patrickgue/fsimcockpit/Models/ai/images/1b0a5739ef15379fbf4dc0a945f766ee.png

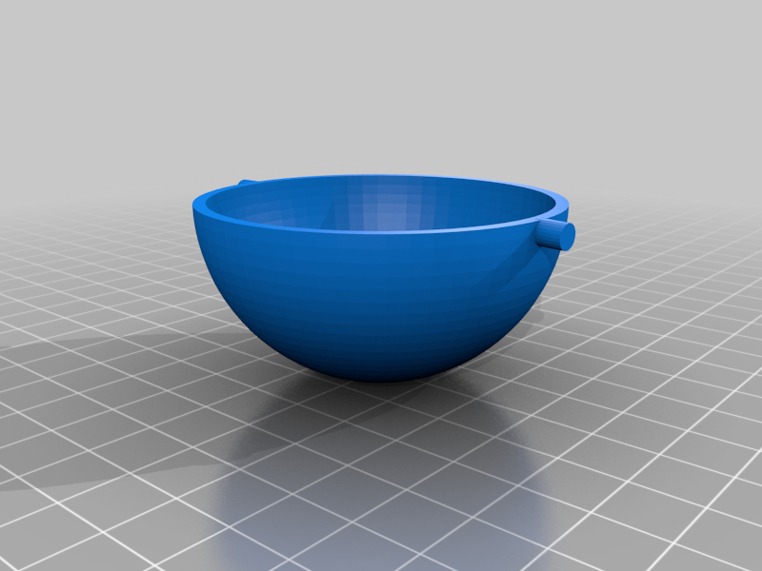
Models/ai/images/1b0a5739ef15379fbf4dc0a945f766ee.png
