patrickgue/fsimcockpit/Models/ai/images/1e4439b8b44afa9f4f896fb0e1ca348d.png

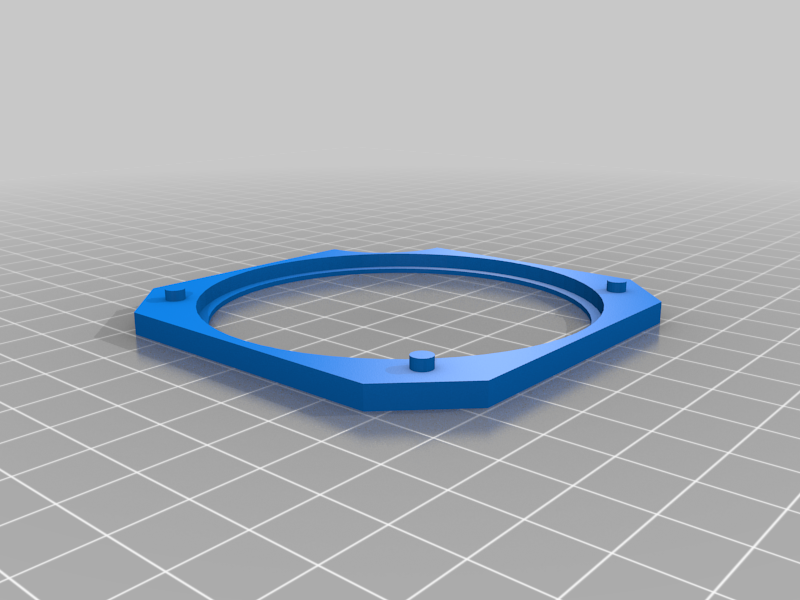
Models/ai/images/1e4439b8b44afa9f4f896fb0e1ca348d.png
