patrickgue/fsimcockpit/Models/ai/images/02c6412a4f1afc17a5a2229d6d05a12a.png

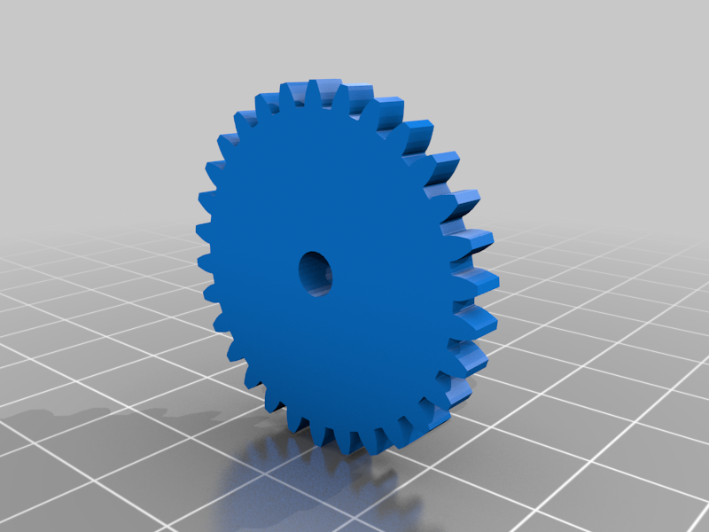
Models/ai/images/02c6412a4f1afc17a5a2229d6d05a12a.png
