patrickgue/fsimcockpit/Models/ai/images/3a77de7b587de0e3436b201ad0739e6e.png

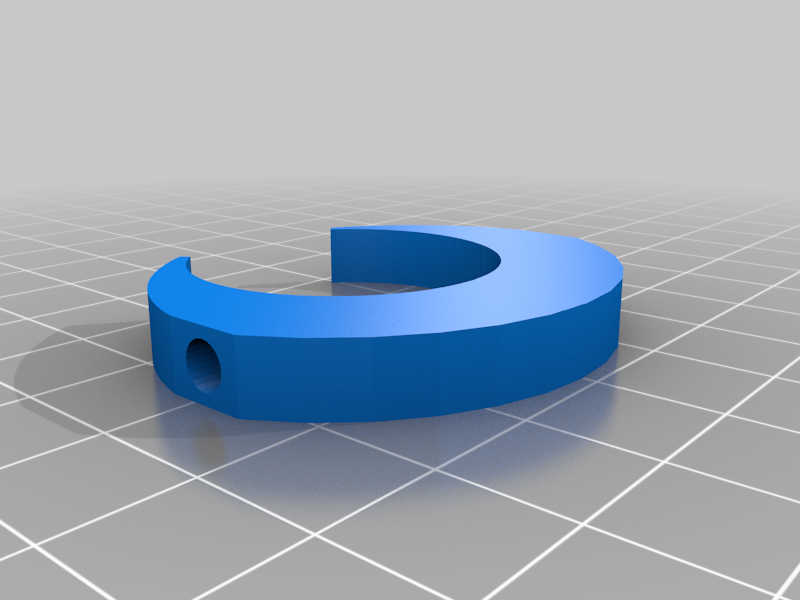
Models/ai/images/3a77de7b587de0e3436b201ad0739e6e.png
