patrickgue/fsimcockpit/Models/ai/images/6ea9e44ec9cb2694fbe0ab6ae0526416.png

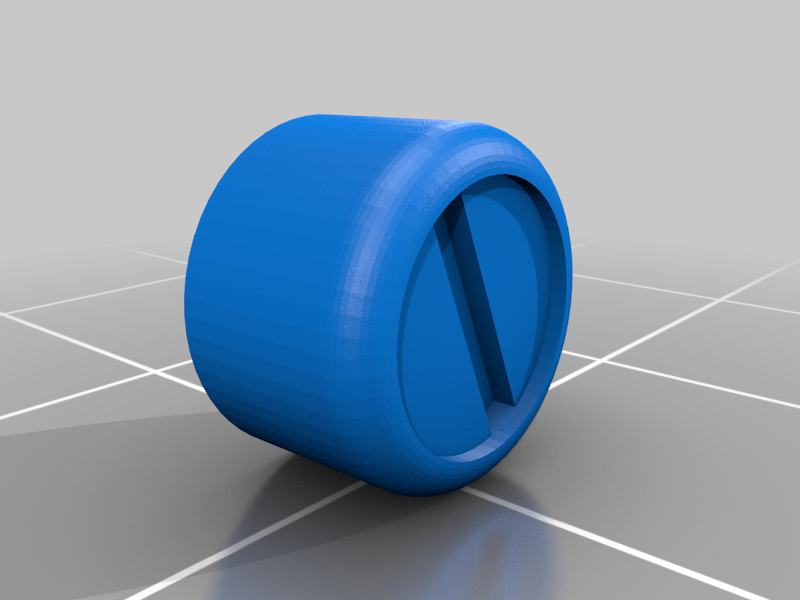
Models/ai/images/6ea9e44ec9cb2694fbe0ab6ae0526416.png
