patrickgue/fsimcockpit/Models/ai/images/9bbd3e1e0be2ce5231e5939fdd35f54f.png

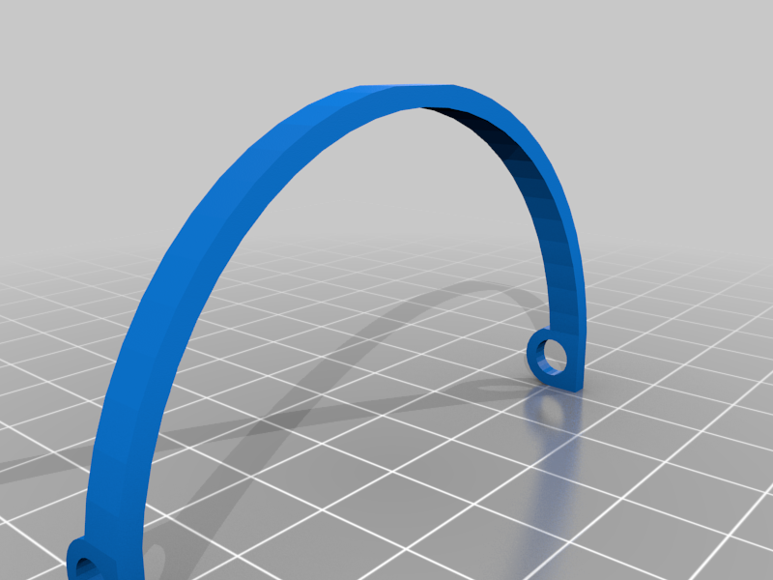
Models/ai/images/9bbd3e1e0be2ce5231e5939fdd35f54f.png
