patrickgue/fsimcockpit/Models/ai/images/9d65d15d78d8a212db82cd6689131c01.png

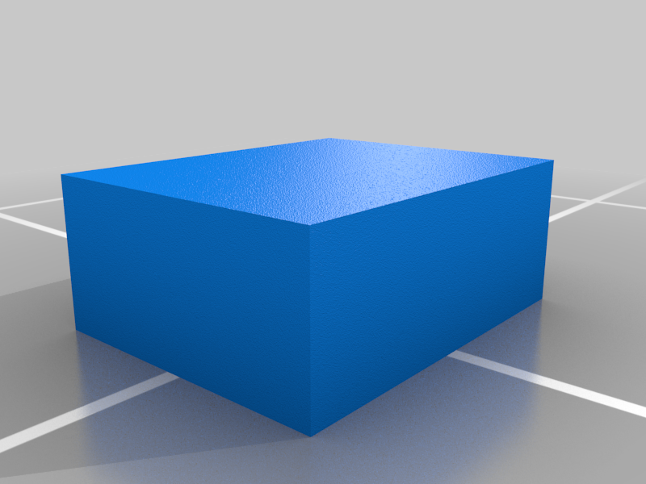
Models/ai/images/9d65d15d78d8a212db82cd6689131c01.png
