patrickgue/fsimcockpit/Models/ai/images/497fff0eb1eede1f7c7d94e4efdf7a6d.png

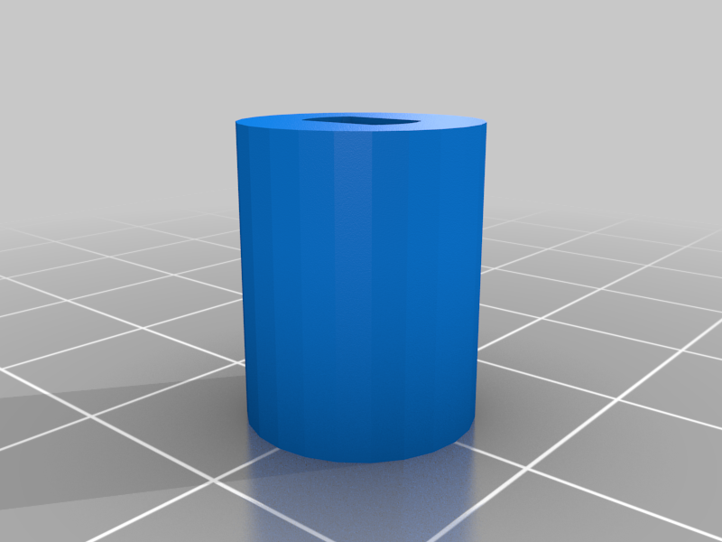
Models/ai/images/497fff0eb1eede1f7c7d94e4efdf7a6d.png
