patrickgue/fsimcockpit/Models/ai/images/996b78e1af478235ca2ef95079a0255b.png

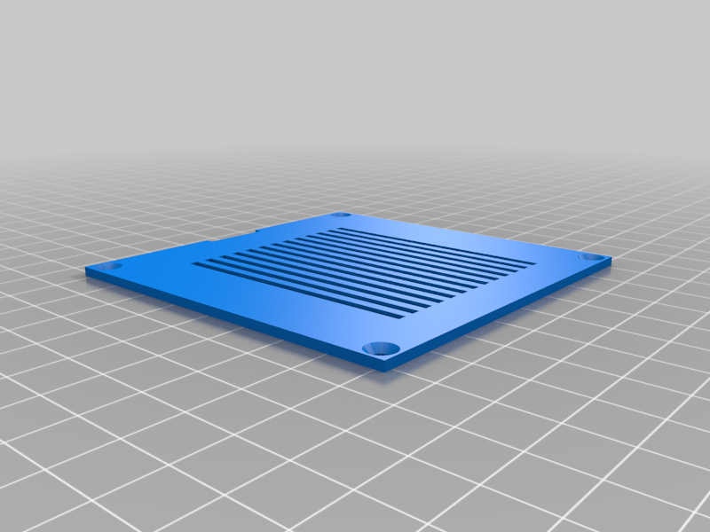
Models/ai/images/996b78e1af478235ca2ef95079a0255b.png
