patrickgue/fsimcockpit/Models/ai/images/b6f1c5f29eb557028f5184abd817bedb.png

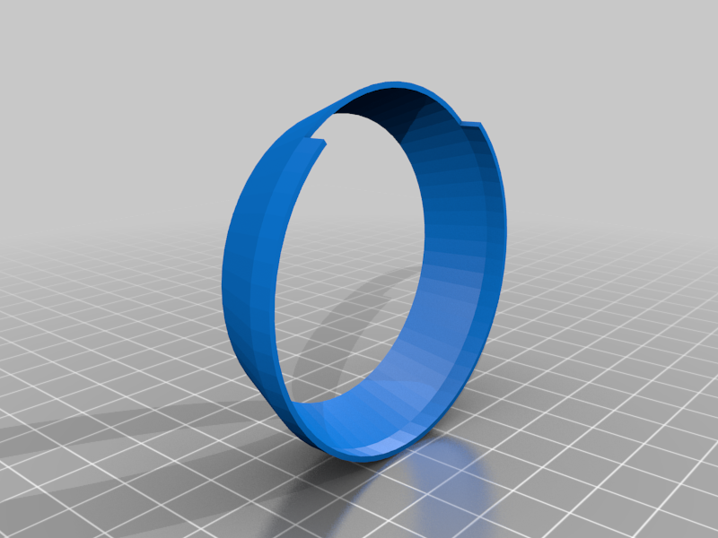
Models/ai/images/b6f1c5f29eb557028f5184abd817bedb.png
