patrickgue/fsimcockpit/Models/ai/images/Bank_Angle.jpg

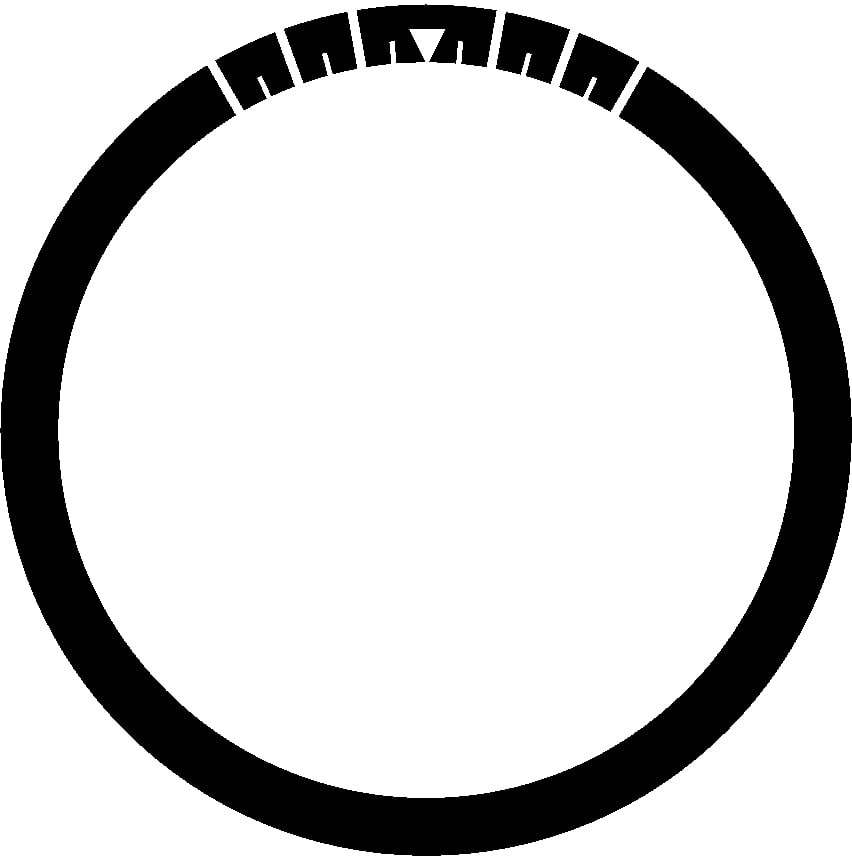
Models/ai/images/Bank_Angle.jpg
