patrickgue/fsimcockpit/Models/ai/images/de8ef12720e9b7bbc3c7db81c315f879.png

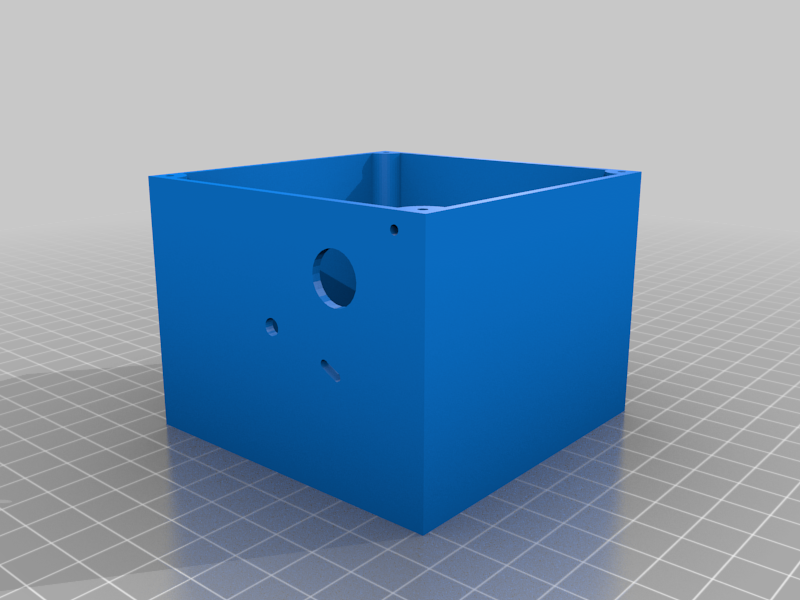
Models/ai/images/de8ef12720e9b7bbc3c7db81c315f879.png
