patrickgue/fsimcockpit/Models/ai/images/df47952833d656812641ab8248f8aa33.png

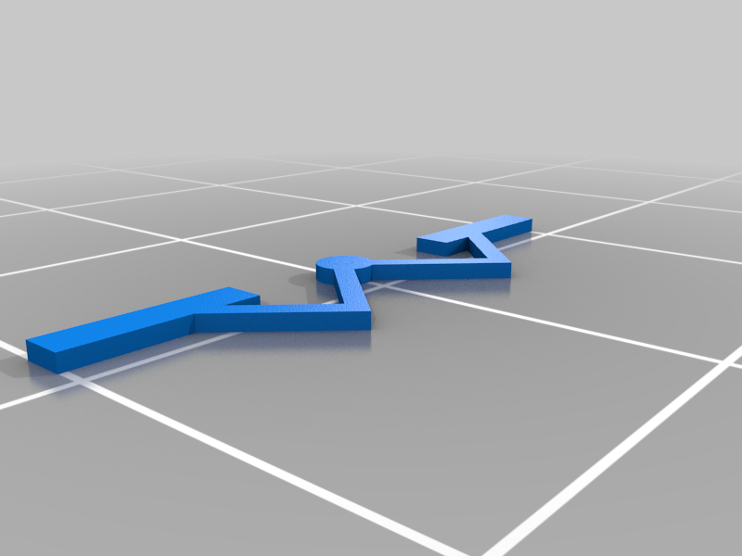
Models/ai/images/df47952833d656812641ab8248f8aa33.png
