patrickgue/fsimcockpit/Models/ai/images/Download_3.png

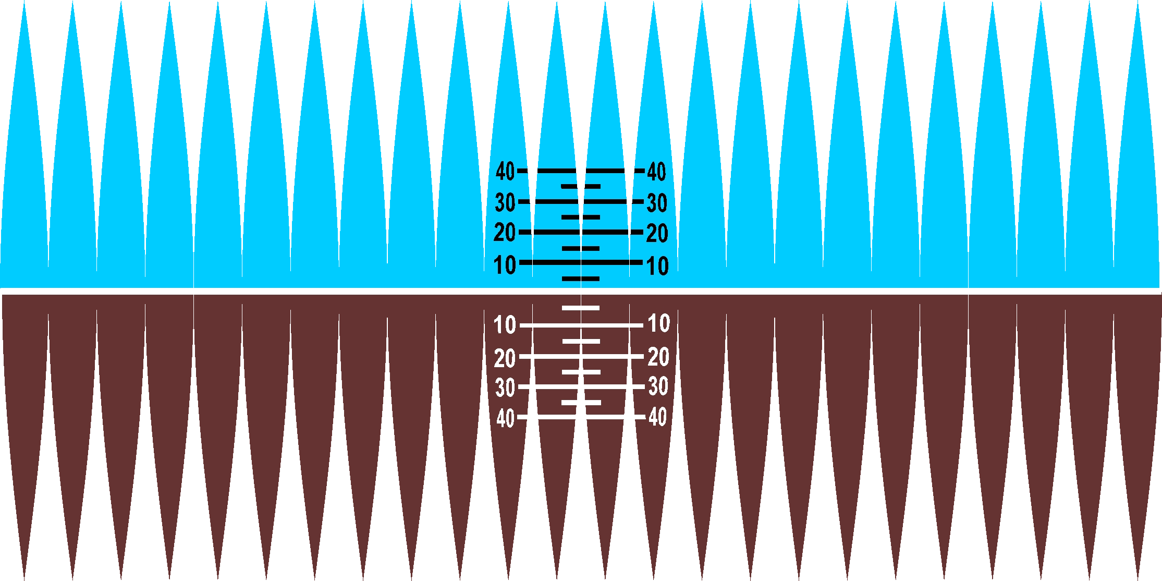
Models/ai/images/Download_3.png
