patrickgue/fsimcockpit/Models/tc/images/941b54a7-352c-473a-afa9-f229a11ba6b9.jpg

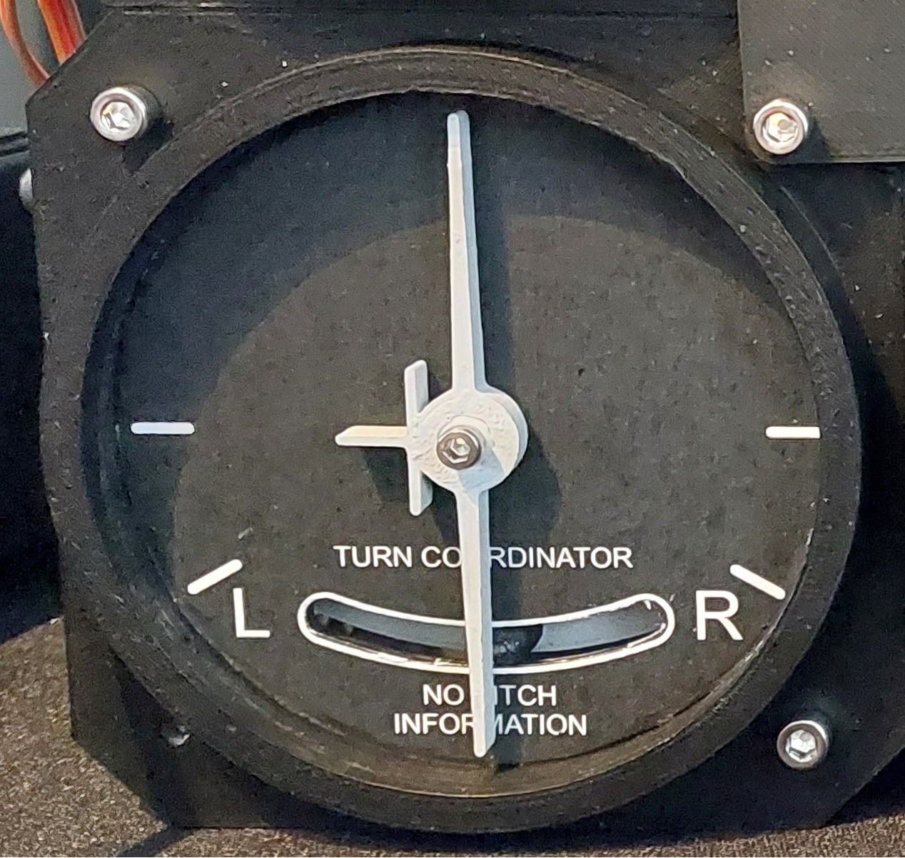
Models/tc/images/941b54a7-352c-473a-afa9-f229a11ba6b9.jpg
