patrickgue/fsimcockpit/Models/tc/images/90883c77-fded-4542-9856-6aad363a4fbb.png

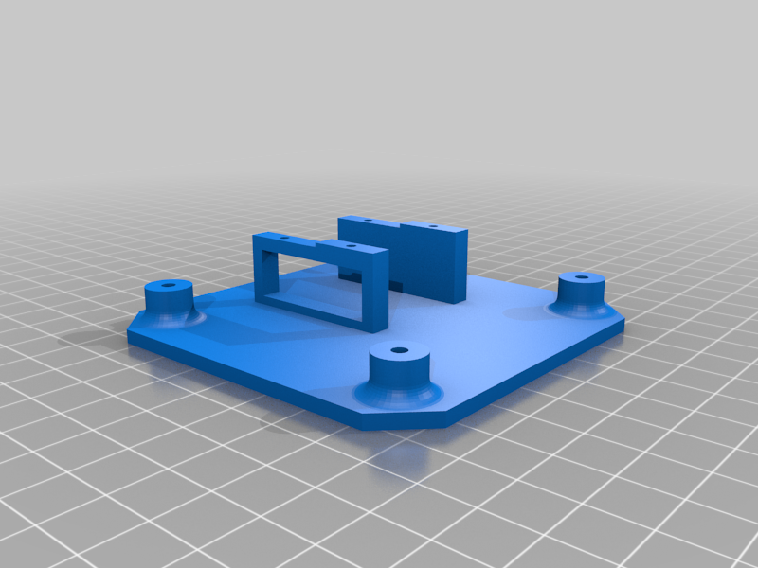
Models/tc/images/90883c77-fded-4542-9856-6aad363a4fbb.png
