patrickgue/fsimcockpit/Models/tc/images/bf2bf9c6-6777-4b66-9cf1-4f259d72259a.png

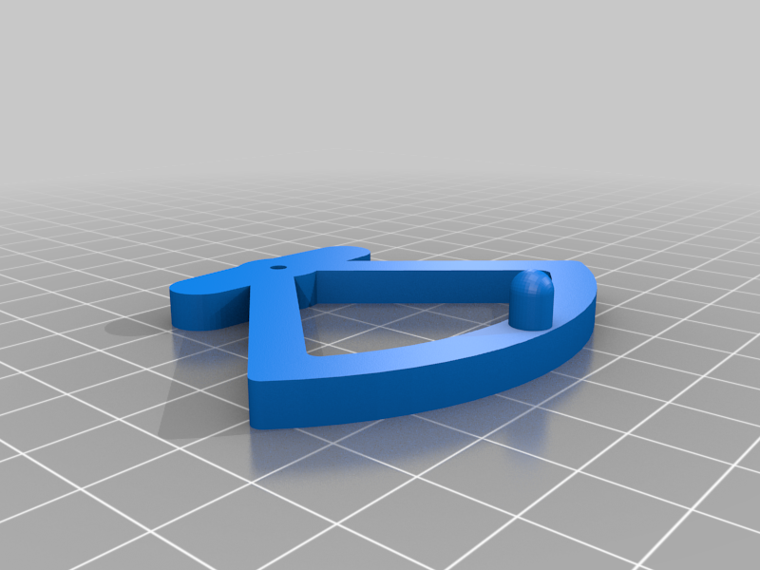
Models/tc/images/bf2bf9c6-6777-4b66-9cf1-4f259d72259a.png
