patrickgue/fsimcockpit/Models/vsi_as/Vertical velocity indicator for flight simulator - 6637015/images/29d1b277-3d54-4ff1-81d7-2cb92e95f4e1.jpg

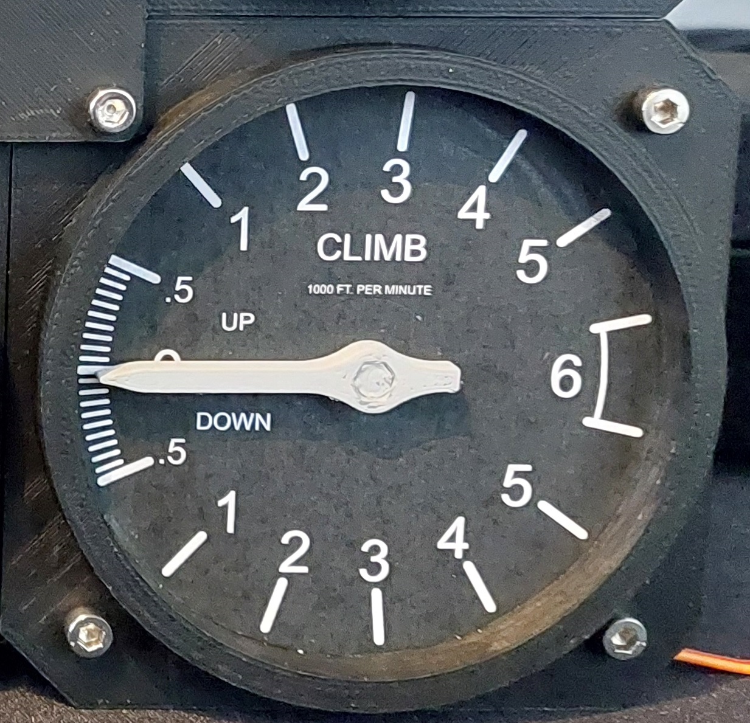
Models/vsi_as/Vertical velocity indicator for flight simulator - 6637015/images/29d1b277-3d54-4ff1-81d7-2cb92e95f4e1.jpg
