patrickgue/fsimcockpit/Models/vsi_as/Vertical velocity indicator for flight simulator - 6637015/images/589b4585-1702-4620-8059-6b79ba6a5d64.png

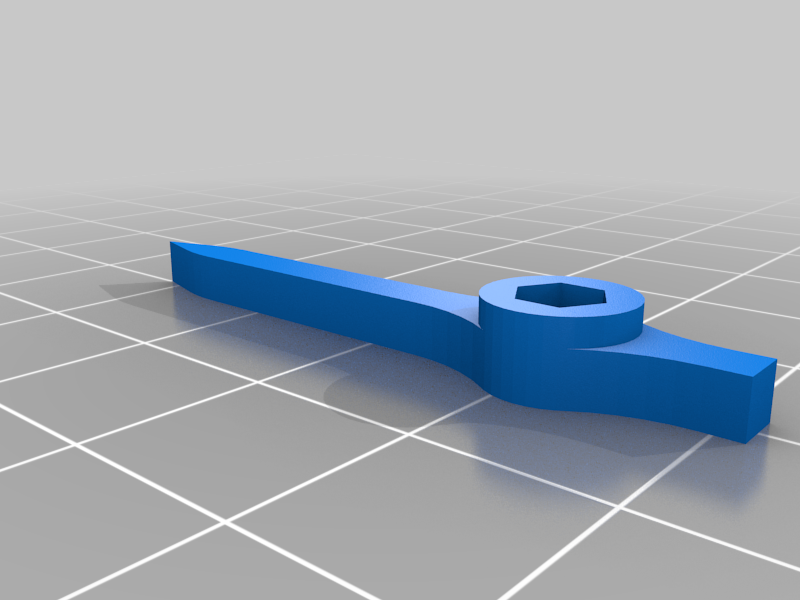
Models/vsi_as/Vertical velocity indicator for flight simulator - 6637015/images/589b4585-1702-4620-8059-6b79ba6a5d64.png
