patrickgue/fsimcockpit/Models/vsi_as/Vertical velocity indicator for flight simulator - 6637015/images/c1e8b9d2-94b4-4caa-8674-2cb49150a157.png

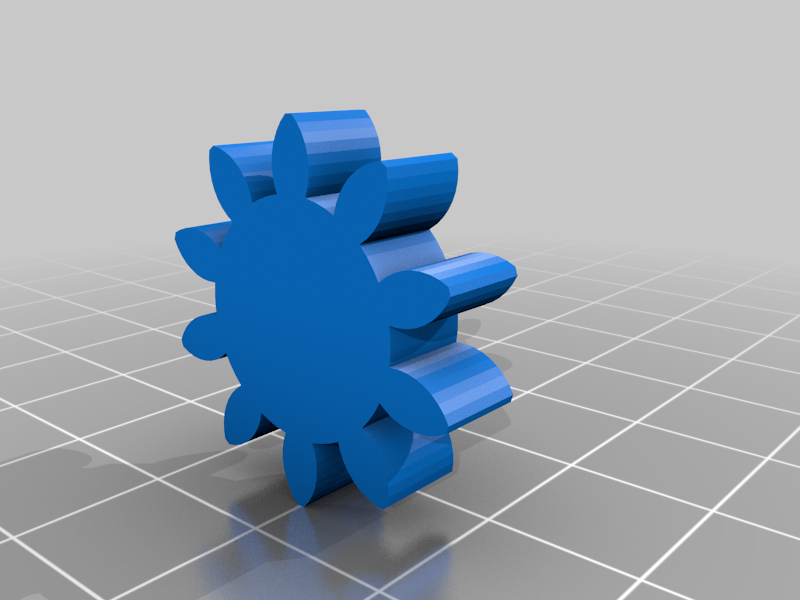
Models/vsi_as/Vertical velocity indicator for flight simulator - 6637015/images/c1e8b9d2-94b4-4caa-8674-2cb49150a157.png
