patrickgue/fsimcockpit/Models/ai/files/Kugelstift.stl

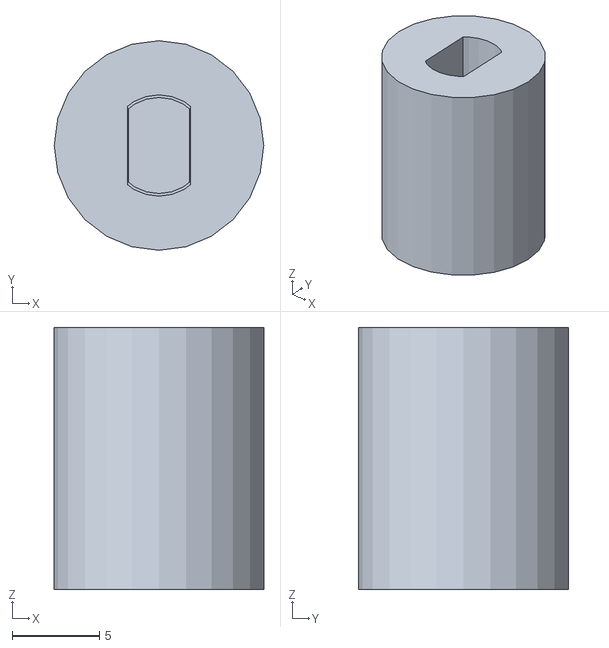
[picture p39: CAD file, 2026-08-16]
Models/ai/files/Kugelstift.stl
12.0 x 12.0 x 15.0
