patrickgue/fsimcockpit/Models/hi/dial.stl

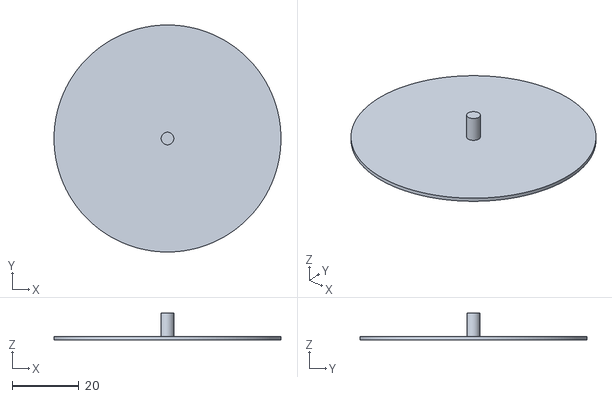
[picture p40: CAD file, 2026-08-27]
Models/hi/dial.stl
68.0 x 68.0 x 8.00
