patrickgue/fsimcockpit/Models/tc/files/aircraft.STL

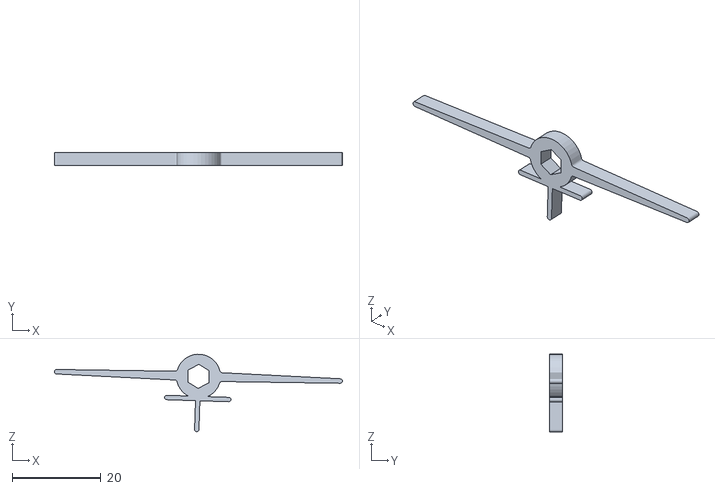
[picture p41: CAD file, 2026-08-21]
Models/tc/files/aircraft.STL
65.0 x 3.00 x 17.5
