patrickgue/fsimcockpit/Models/vsi_as/Vertical velocity indicator for flight simulator - 6637015/files/needle_gear.STL

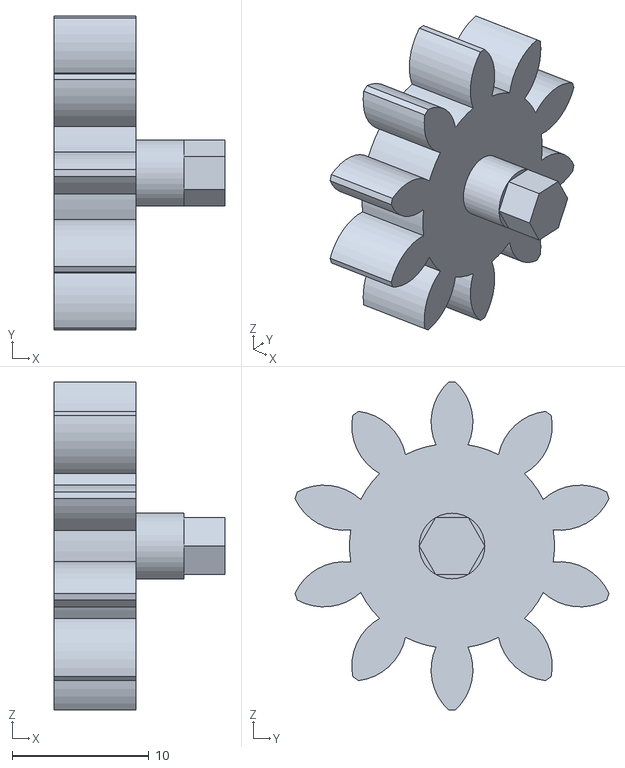
[picture p42: CAD file, 2026-07-31]
Models/vsi_as/Vertical velocity indicator for flight simulator - 6637015/files/needle_gear.STL
12.5 x 23.0 x 24.0
