patrickgue/fsimcockpit/Models/ai/files/Gehaeuse.stl

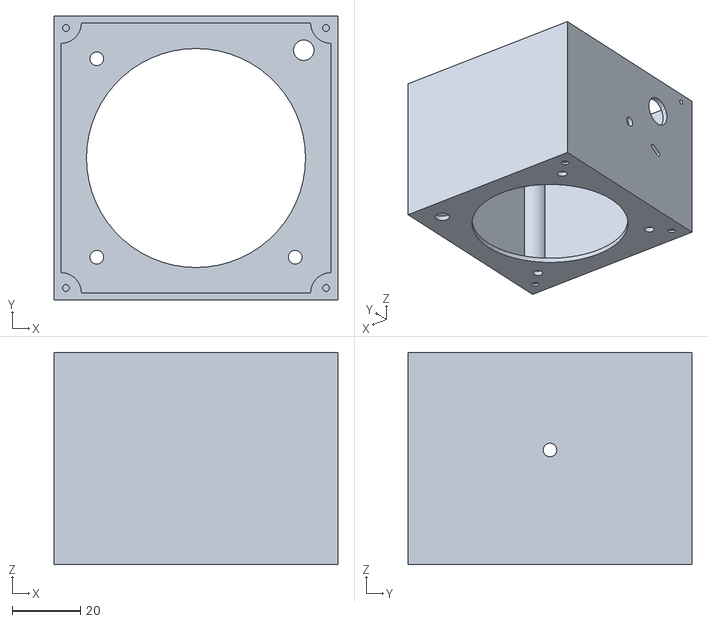
[picture p43: CAD file, 2026-08-16]
Models/ai/files/Gehaeuse.stl
83.0 x 83.0 x 62.0
