patrickgue/fsimcockpit/Models/hi/stepper_mount.stl

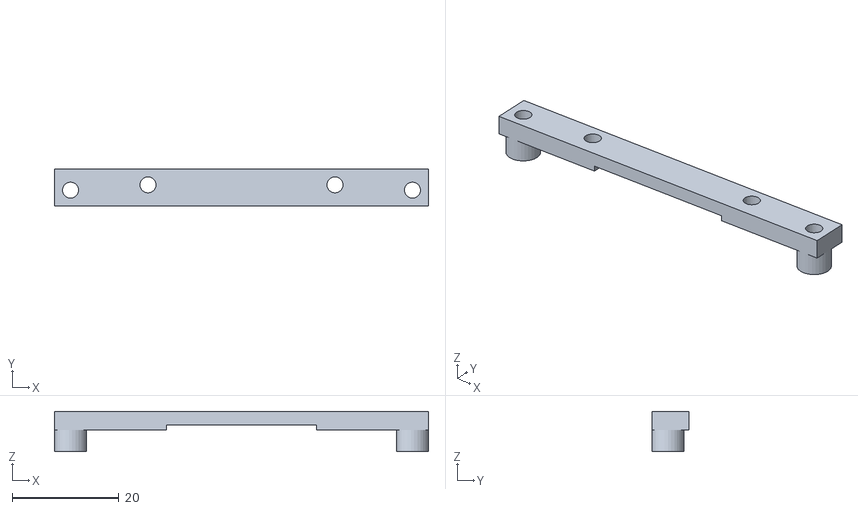
[picture p44: CAD file, 2026-08-27]
Models/hi/stepper_mount.stl
70.0 x 7.00 x 7.50
