patrickgue/fsimcockpit/Models/ai/files/Blende_innen.stl

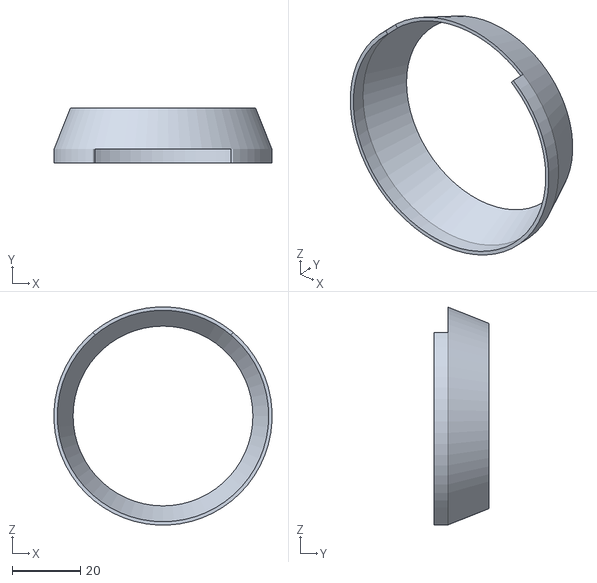
[picture p45: CAD file, 2026-08-16]
Models/ai/files/Blende_innen.stl
63.9 x 16.0 x 63.9
