patrickgue/fsimcockpit/Models/ai/files/Zeiger.stl

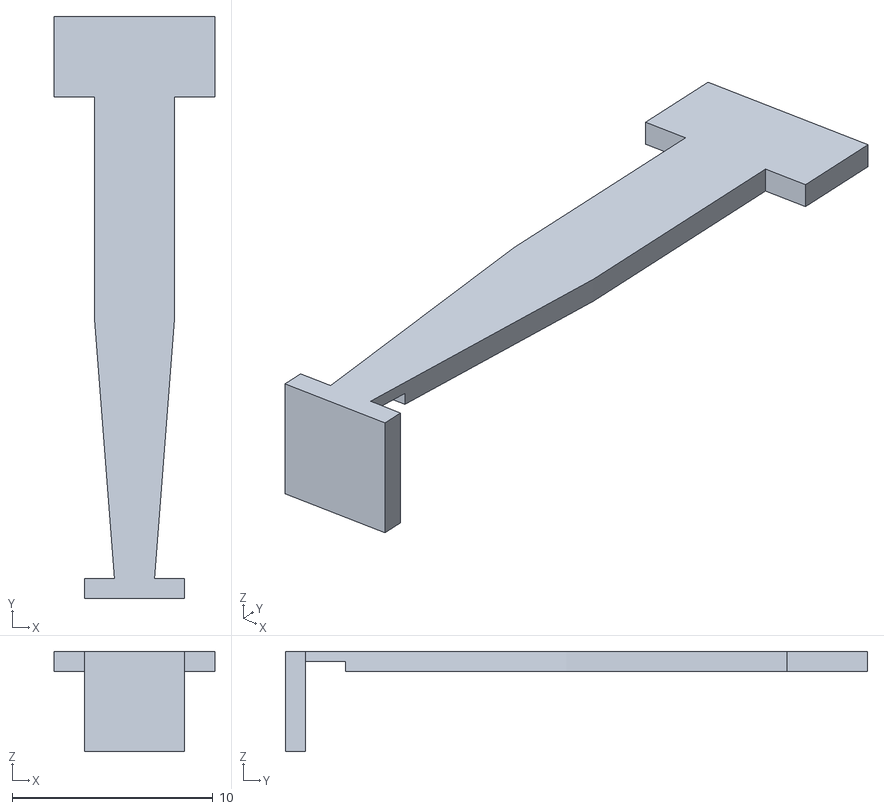
[picture p46: CAD file, 2026-08-16]
Models/ai/files/Zeiger.stl
8.00 x 29.0 x 5.00
