patrickgue/fsimcockpit/Models/ai/files/Zahnrad1.stl

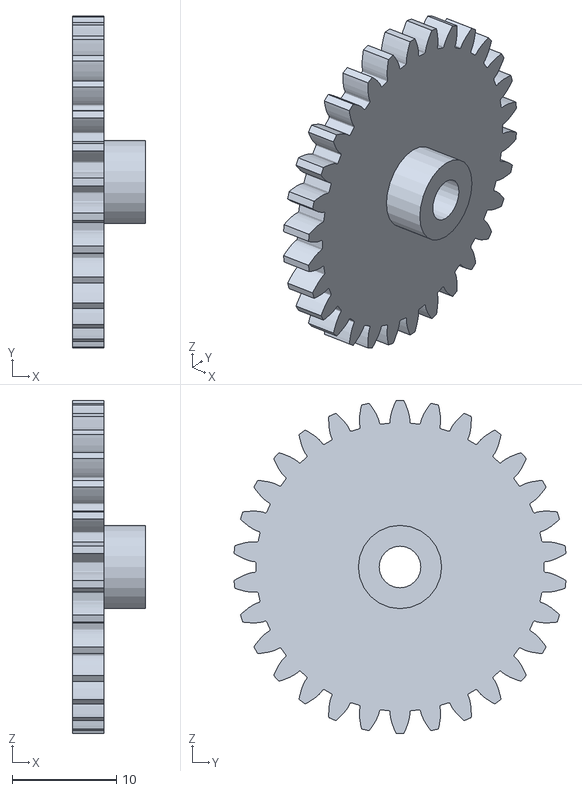
[picture p47: CAD file, 2026-08-16]
Models/ai/files/Zahnrad1.stl
7.00 x 31.9 x 32.0
