patrickgue/fsimcockpit/Models/ai/files/Buegel.stl

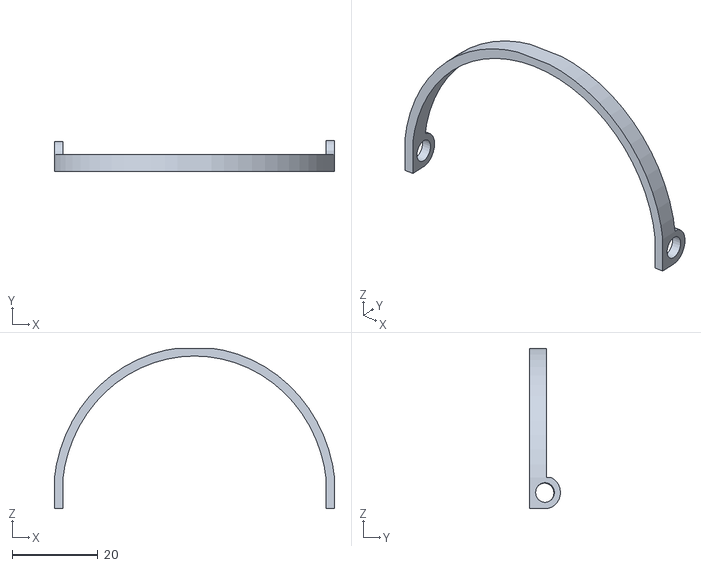
[picture p48: CAD file, 2026-08-16]
Models/ai/files/Buegel.stl
65.5 x 7.24 x 37.5
