patrickgue/fsimcockpit/Models/ai/files/Zahnrad2.stl

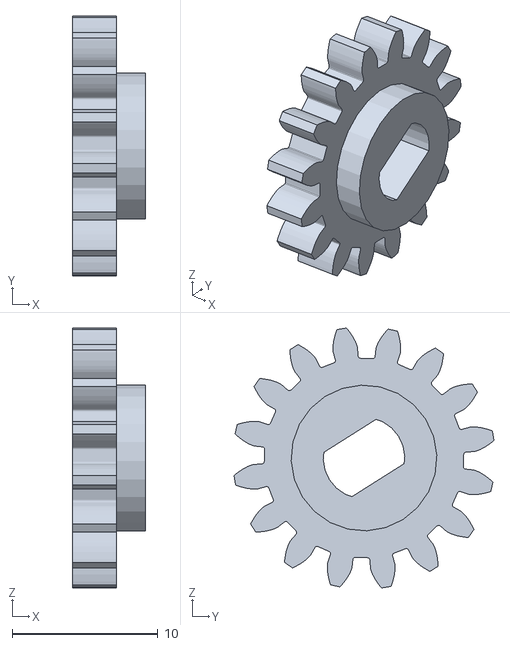
[picture p49: CAD file, 2026-08-16]
Models/ai/files/Zahnrad2.stl
5.00 x 17.8 x 17.8
