patrickgue/fsimcockpit/Models/ai/files/Zeigerblaettchen.stl

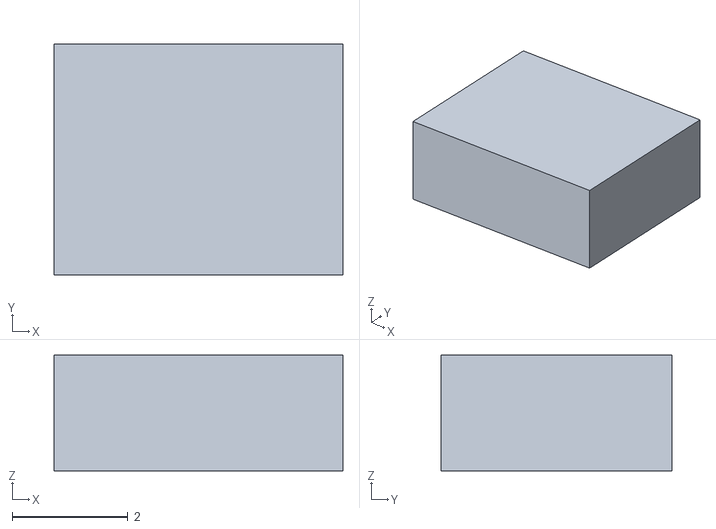
[picture p50: CAD file, 2026-08-16]
Models/ai/files/Zeigerblaettchen.stl
5.00 x 4.00 x 2.00
