patrickgue/fsimcockpit/Models/ai/files/Horizontmarkierung.stl

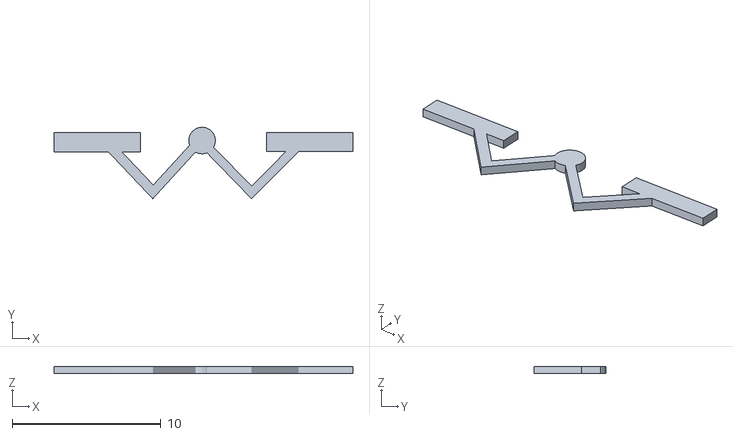
[picture p51: CAD file, 2026-08-16]
Models/ai/files/Horizontmarkierung.stl
20.1 x 4.81 x 0.5
