patrickgue/fsimcockpit/Models/ai/files/Frontblend.stl

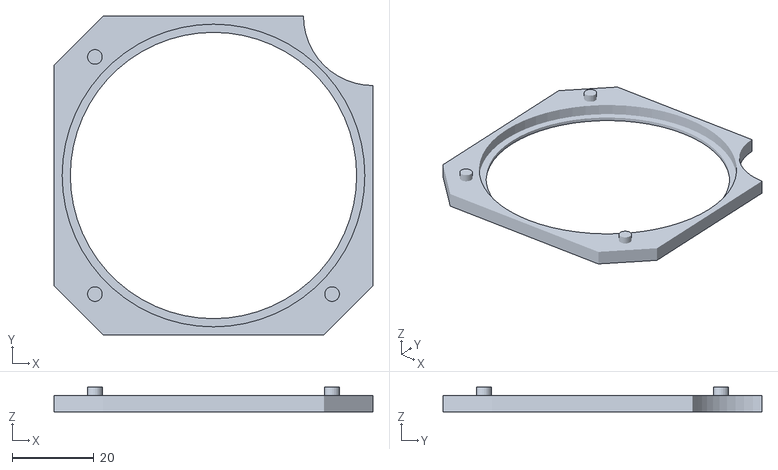
[picture p52: CAD file, 2026-08-16]
Models/ai/files/Frontblend.stl
78.0 x 78.0 x 6.00
