patrickgue/fsimcockpit/Models/vsi_as/Standoff.scad

$fn=64;

difference() {
    cylinder(d=10,h=40-7);
    cylinder(d=2,h=40-7);
}
