patrickgue/fsimcockpit/ArduinoDriver/codes.h

#ifndef codes_h
#define codes_h

#define VSI                              0x10
#define VSI_CALIBR_ZERO                  0x11
#define VSI_CALIBR_PLUS5                 0x12
#define VSI_CALIBR_MINUS5                0x13
#define HI                               0x20
#define HI_CALIBR_ZERO                   0x21
#define SPEED                            0x30
#define SPEED_CALIBR_ZERO                0x31
#define SPEED_CALIBR_HUNDRED             0x32
#define ALT                              0x40
#define ALT_CALIBR_HUNDREDS_ZERO         0x41
#define ALT_CALIBR_THOUSANDS_ZERO        0x42
#define ALT_CALIBR_TENTHOUSANDS_ZERO     0x43
#define TS_TURN                          0x50
#define TS_TURN_CALIBR_ZERO              0x51
#define TS_TURN_CALIBR_LEFTTURN          0x52
#define TS_TURN_CALIBR_RIGHTTURN         0x53
#define TS_SLIP                          0x54
#define TS_SLIP_CALIBR_ZERO              0x55
#define TS_SLIP_CALIBR_LEFT              0x56
#define TS_SLIP_CALIBR_RIGHT             0x57
#define AI_PITCH                         0x60
#define AI_PITCH_CALIBR_ZERO             0x61
#define AI_PITCH_CALIBR_20UP             0x62
#define AI_PITCH_CALIBR_20DOWN           0x63
#define AI_ROLL                          0x64
#define AI_ROLL_CALIBR_ZERO              0x65
#define AI_ROLL_CALIBR_20LEFT            0x66
#define AI_ROLL_CALIBR_20RIGHT           0x67
#define ERROR                            0xFF

#endif
